lutzer/midi_clock/src/debug.rs

#[macro_export]
macro_rules! debug {
  ($($rest:tt)*) => {
    #[cfg(feature = "debug")]
    self::debug::debug_methods::debug_print($($rest)*)
  }
}

#[cfg(feature = "debug")] 
pub mod debug_methods {
  use crate::{CONTEXT};
  use crate::utils::{u16_to_string, i16_to_string, u32_to_string};
  use crate::statemachine::State;
  use core::str;
  use cortex_m::interrupt::{CriticalSection};

  pub trait Stringable<'a> {
    fn into_string(self) -> &'a str;
  }
  
  impl<'a> Stringable<'a> for &'a str {
    fn into_string(self) -> &'a str {
      return self
    }
  }
  
  impl<'a> Stringable<'a> for u16 {
    fn into_string(self) -> &'a str {
      let s = u16_to_string(self);
      return s
    }
  }

  impl<'a> Stringable<'a> for u32 {
    fn into_string(self) -> &'a str {
      let s = u32_to_string(self);
      return s
    }
  }
  
  impl<'a> Stringable<'a> for i16 {
    fn into_string(self) -> &'a str {
      let s = i16_to_string(self);
      return s
    }
  }
  
  impl<'a> Stringable<'a> for bool {
    fn into_string(self) -> &'a str {
      return if self { "1" } else { "0" }
    }
  }

  impl<'a> Stringable<'a> for State {
    fn into_string(self) -> &'a str {
      const BUFFER_LENGTH: usize = 16;
      static mut buffer: [u8;BUFFER_LENGTH] = [0; BUFFER_LENGTH];

      unsafe fn add_number(val: u16, i: &mut usize) {
        let string = u16_to_string(val);
        buffer[*i..*i+string.len()].copy_from_slice(string.as_bytes());
        *i += string.len();
      }

      unsafe fn add_string(s: &str, i: &mut usize) {
        buffer[*i..*i+s.len()].copy_from_slice(s.as_bytes());
        *i += s.len();
      }

      unsafe {
        let mut i = 0;
        add_string("b", &mut i);
        add_number(self.bpm, &mut i);
        add_string(" r", &mut i);
        add_number(self.running as u16, &mut i);
        add_string(" m", &mut i);
        add_number(self.clock_trigger_multiplier as u16, &mut i);
        add_string(" d", &mut i);
        add_number(self.clock_divisions[0] as u16, &mut i);
        add_string(",", &mut i);
        add_number(self.clock_divisions[1] as u16, &mut i);
        for i in i..BUFFER_LENGTH {
          buffer[i] = ' ' as u8;
        }
        return str::from_utf8_unchecked(&buffer);
      }
    }
  }
  
  pub fn debug_print<'a, T>(s: T) where T : Stringable<'a> {
    cortex_m::interrupt::free(|cs| {
      let mut context = CONTEXT.borrow(cs).borrow_mut();
      context.as_mut().map(|ctx| {
        let serial =  &mut ctx.serial;
        serial.write_str(1,"[DEBUG] ").ok();
        serial.write_str(1,s.into_string()).ok();
        serial.write_str(1,"\n\r").ok();
      });
    });
  }
}
